mike-rankin/GPS_Board/Code/GPS_Cube/data.h

/* 
 * This file contains all the static arrays to draw things in the display.
 */


// GPS Logo
prog_uchar logo [] PROGMEM = {
0x00, 0x00, 0x00, 0x00, 0x00, 0x00, 0x00, 0x00, 0x00, 0x00, 0x00, 0x00, 0x00, 0x00, 0x00, 0x00,
0x00, 0x00, 0x00, 0x00, 0x00, 0x00, 0x00, 0x00, 0x00, 0x00, 0x00, 0x00, 0x00, 0x00, 0x00, 0x00,
0x00, 0x00, 0x00, 0x00, 0x00, 0x00, 0x00, 0x00, 0x80, 0xC0, 0xE0, 0x70, 0x38, 0x1C, 0x1C, 0x38,
0x70, 0xE0, 0xC0, 0x80, 0x00, 0x00, 0x00, 0x00, 0x00, 0x00, 0x00, 0x00, 0x00, 0x00, 0x00, 0x00,
0x00, 0x00, 0x00, 0x00, 0x00, 0x00, 0x00, 0x00, 0x00, 0x00, 0x00, 0x00, 0x00, 0x00, 0x00, 0x00,
0x00, 0x00, 0x00, 0x00, 0x00, 0x00, 0x00, 0x00, 0x00, 0x00, 0x00, 0x00, 0x00, 0x00, 0x00, 0x00,
0x00, 0x00, 0x00, 0x00, 0x00, 0x00, 0x00, 0x00, 0x00, 0x00, 0x00, 0x00, 0x00, 0x00, 0x00, 0x00,
0x00, 0x00, 0x00, 0x00, 0x00, 0x00, 0x00, 0x00, 0x00, 0x00, 0x00, 0x00, 0x00, 0x00, 0x00, 0x00,
0x00, 0x00, 0x00, 0x00, 0x00, 0x00, 0x00, 0x00, 0x00, 0x00, 0x00, 0x00, 0x00, 0x00, 0x00, 0x00,
0x00, 0x00, 0x00, 0x00, 0xC0, 0xF0, 0x38, 0x1C, 0x0C, 0x06, 0x86, 0xC6, 0xCE, 0x7C, 0x60, 0xE0,
0xC0, 0x80, 0x00, 0x70, 0xF8, 0xDC, 0x8E, 0x07, 0x03, 0x07, 0x0E, 0x9C, 0xF8, 0xF0, 0x70, 0x38,
0x1C, 0x0E, 0x07, 0x03, 0x00, 0x00, 0x00, 0x00, 0x00, 0x00, 0x00, 0x00, 0x00, 0x00, 0x00, 0x00,
0x00, 0x00, 0x00, 0x00, 0x00, 0x00, 0x00, 0x00, 0x00, 0x00, 0x00, 0x00, 0x00, 0x00, 0x00, 0x00,
0x00, 0x00, 0x00, 0x00, 0x00, 0x00, 0x00, 0x00, 0x00, 0x00, 0x00, 0x00, 0x00, 0x00, 0x00, 0x00,
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
{0x00,0x7F,0x49,0x49,0x49,0x36,0x00,0x00},
{0x00,0x3E,0x41,0x41,0x41,0x22,0x00,0x00},
{0x00,0x7F,0x41,0x41,0x22,0x1C,0x00,0x00},
{0x00,0x7F,0x49,0x49,0x49,0x41,0x00,0x00},
{0x00,0x7F,0x09,0x09,0x09,0x01,0x00,0x00},
{0x00,0x3E,0x41,0x41,0x51,0x72,0x00,0x00},
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
};
